redswoop/gi-joe-killer-whale/hatch/ref/ebay_hinge_closeup.jpeg

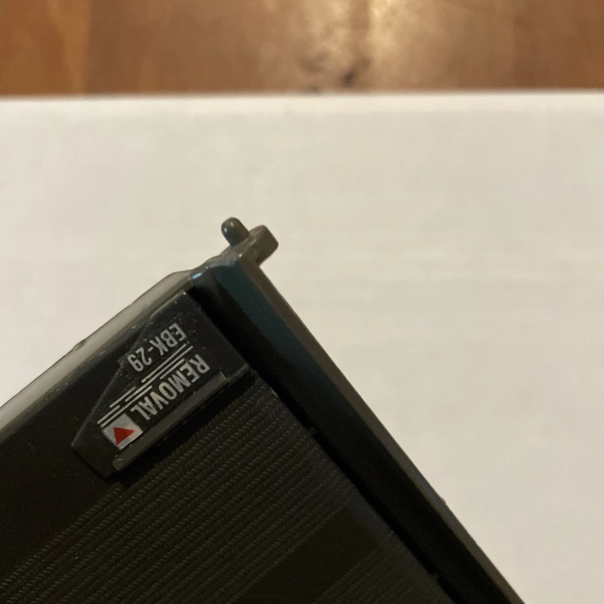
hatch/ref/ebay_hinge_closeup.jpeg
