redswoop/gi-joe-killer-whale/hatch/ref/ebay_outer_face.jpeg

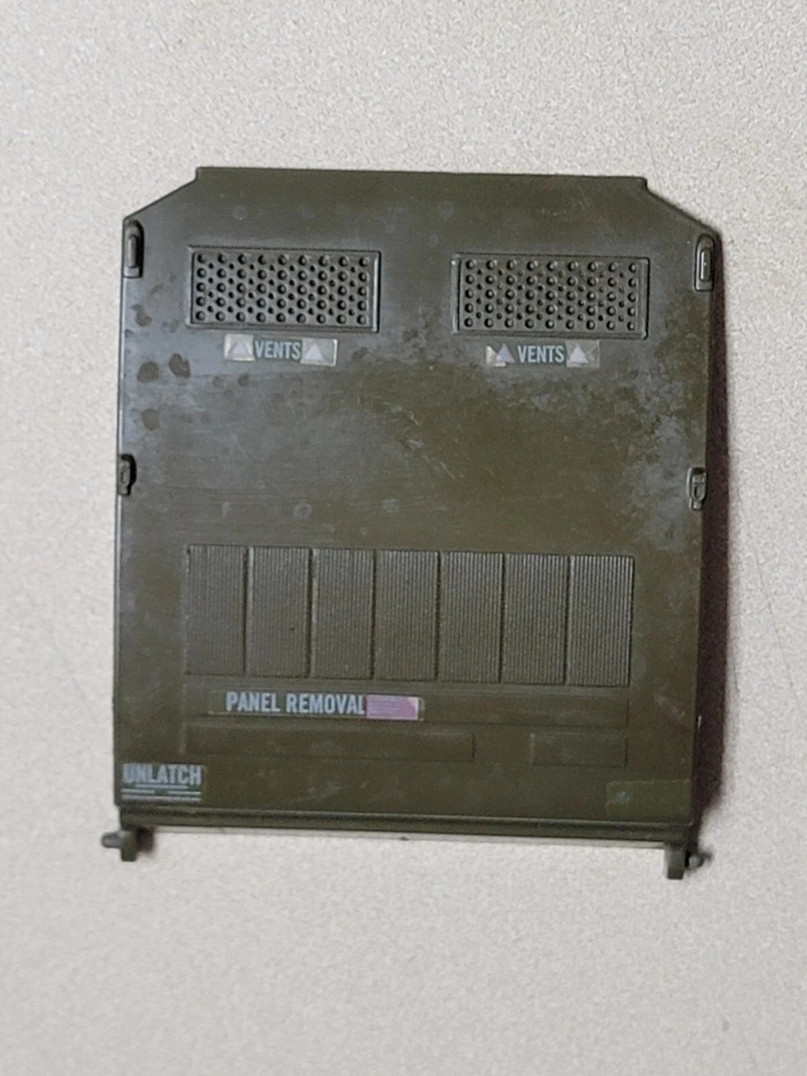
hatch/ref/ebay_outer_face.jpeg
