redswoop/gi-joe-killer-whale/hatch/ref/hull_photo_4.jpeg

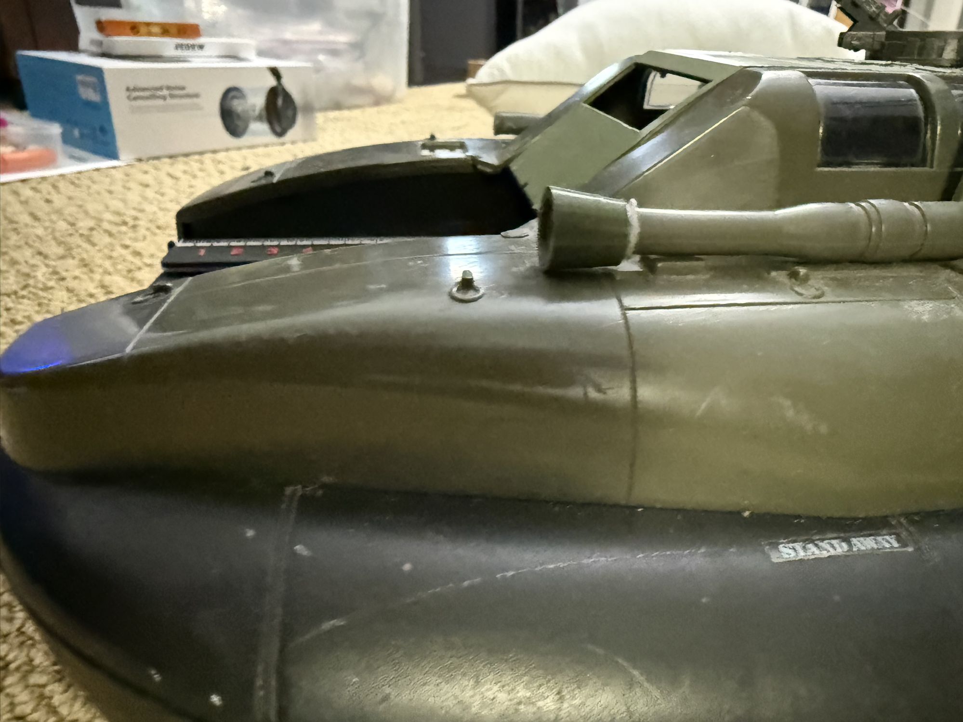
hatch/ref/hull_photo_4.jpeg
