redswoop/gi-joe-killer-whale/hatch/ref/profile_tracing.jpeg

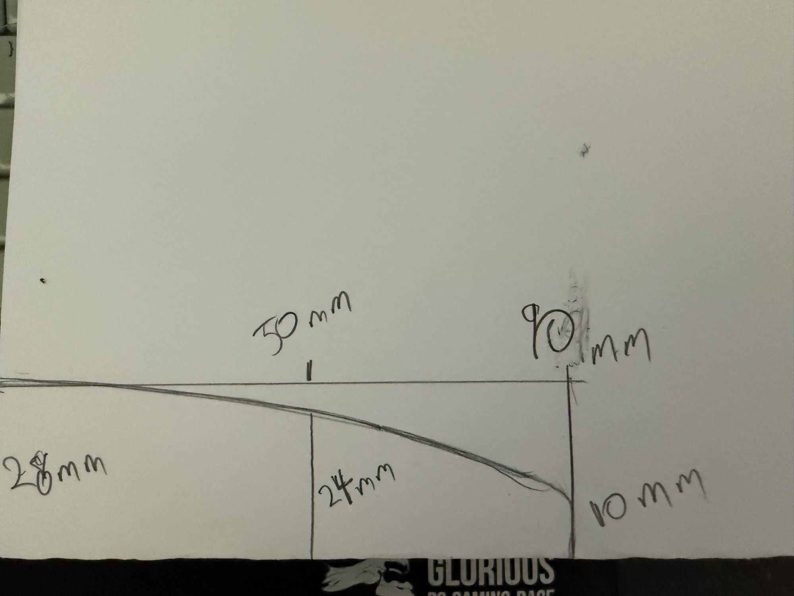
hatch/ref/profile_tracing.jpeg
