redswoop/gi-joe-killer-whale/shroud/stl/vane_right_filpin.stl

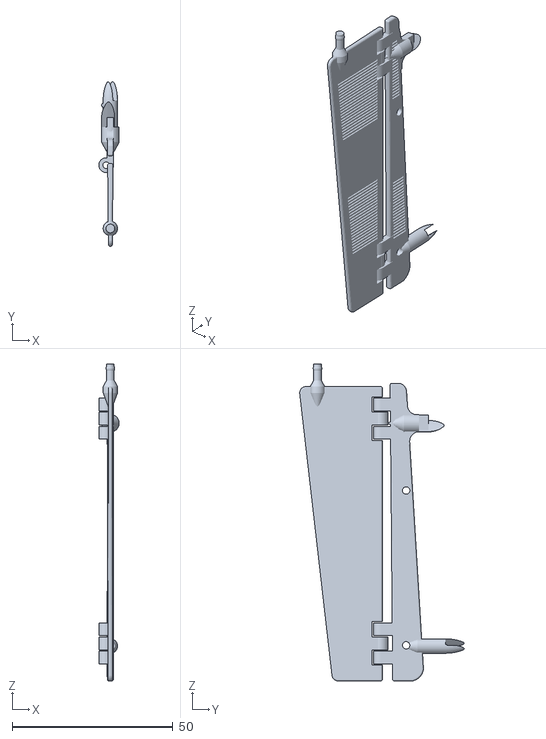
[picture p25: CAD file, 2026-09-13]
shroud/stl/vane_right_filpin.stl
6.35 x 51.3 x 98.7
