redswoop/gi-joe-killer-whale/shroud/stl/hinge_coupon.stl

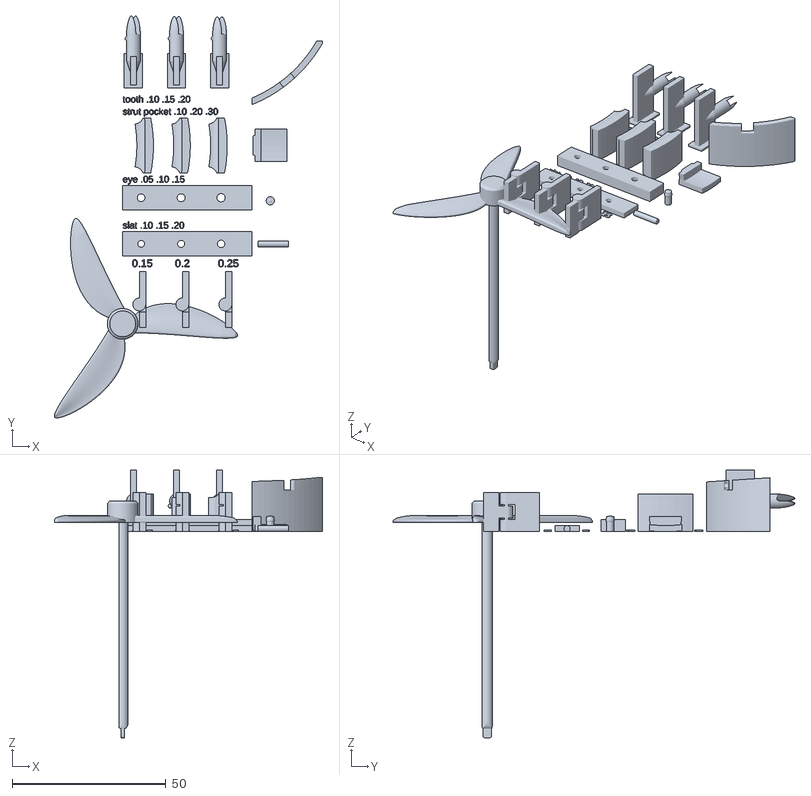
[picture p26: CAD file, 2026-09-12]
shroud/stl/hinge_coupon.stl
87.2 x 130.7 x 87.0
