redswoop/gi-joe-killer-whale/shroud/stl/hinge_coupon_filpin.stl

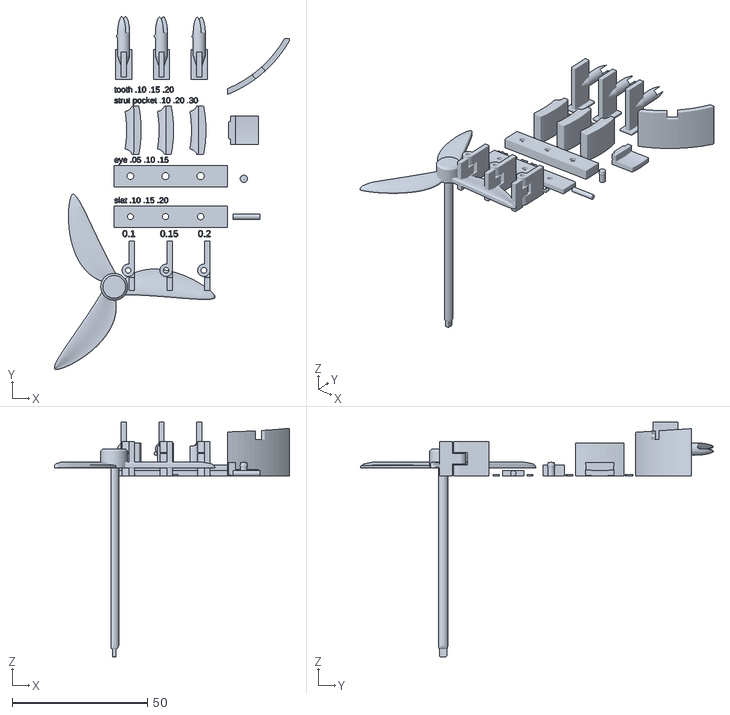
[picture p27: CAD file, 2026-09-12]
shroud/stl/hinge_coupon_filpin.stl
87.2 x 130.7 x 87.0
