redswoop/gi-joe-killer-whale/shroud/stl/tab_coupon.stl

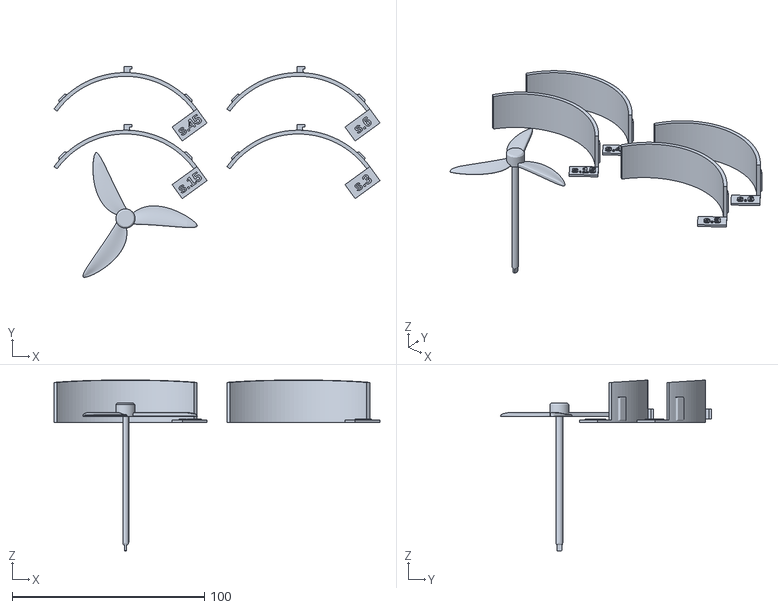
[picture p28: CAD file, 2026-09-12]
shroud/stl/tab_coupon.stl
169.7 x 109.7 x 89.0
