redswoop/gi-joe-killer-whale/shroud/stl/shaft.stl

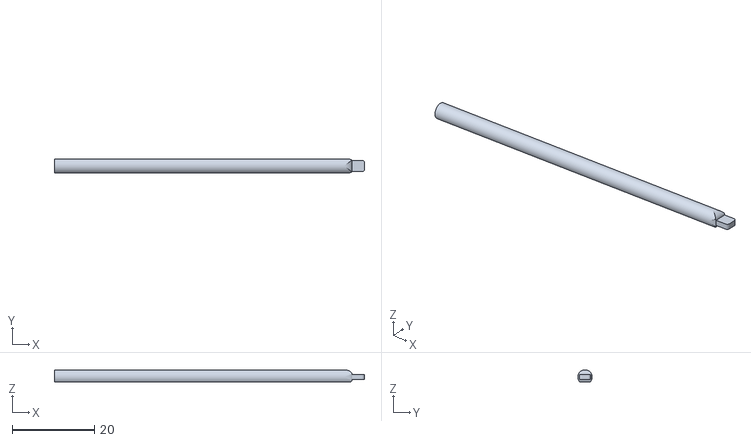
[picture p29: CAD file, 2026-09-12]
shroud/stl/shaft.stl
75.5 x 3.50 x 3.00
