redswoop/gi-joe-killer-whale/shroud/stl/fan.stl

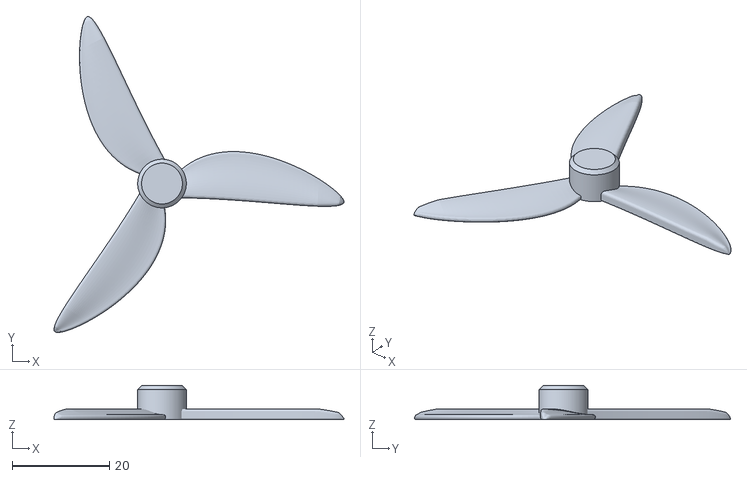
[picture p30: CAD file, 2026-09-12]
shroud/stl/fan.stl
59.6 x 65.0 x 7.00
