redswoop/gi-joe-killer-whale/shroud/stl/slat_fused.stl

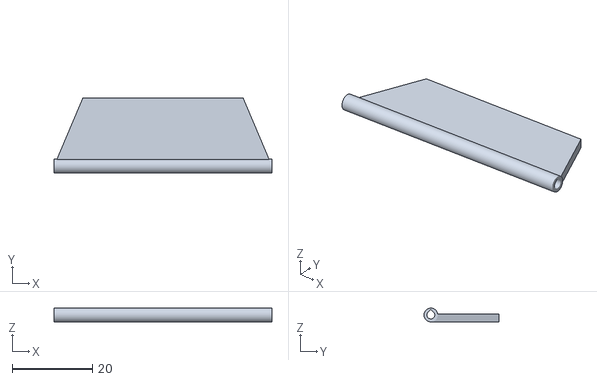
[picture p31: CAD file, 2026-09-12]
shroud/stl/slat_fused.stl
54.4 x 18.7 x 3.45
