redswoop/gi-joe-killer-whale/shroud/stl/shroud_saddle.stl

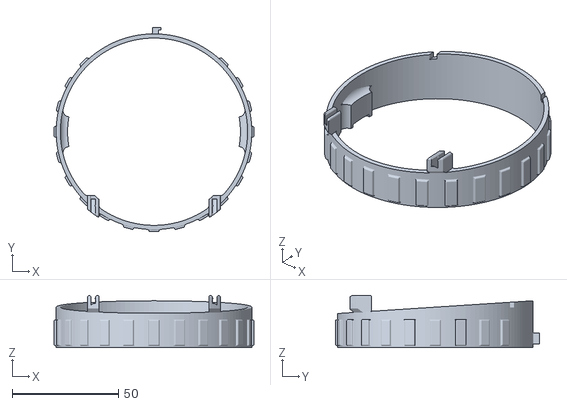
[picture p32: CAD file, 2026-09-11]
shroud/stl/shroud_saddle.stl
94.0 x 96.1 x 24.5
