redswoop/gi-joe-killer-whale/shroud/stl/tie_bar.stl

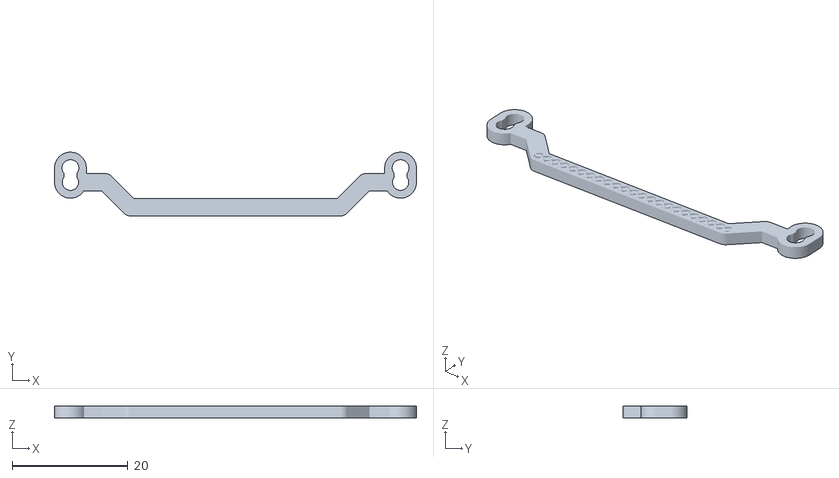
[picture p33: CAD file, 2026-09-11]
shroud/stl/tie_bar.stl
62.5 x 11.0 x 2.00
