redswoop/gi-joe-killer-whale/shroud/stl/slat.stl

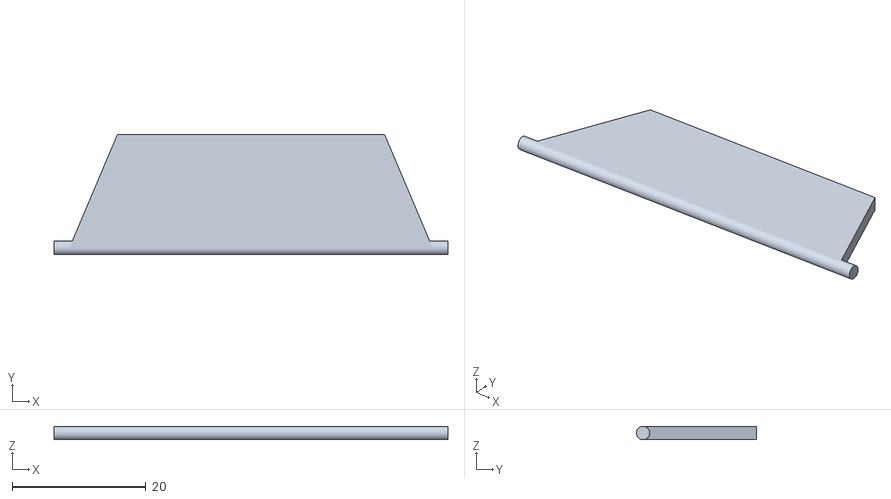
[picture p34: CAD file, 2026-09-11]
shroud/stl/slat.stl
59.0 x 18.0 x 2.00
