redswoop/gi-joe-killer-whale/shroud/stl/strut.3mf

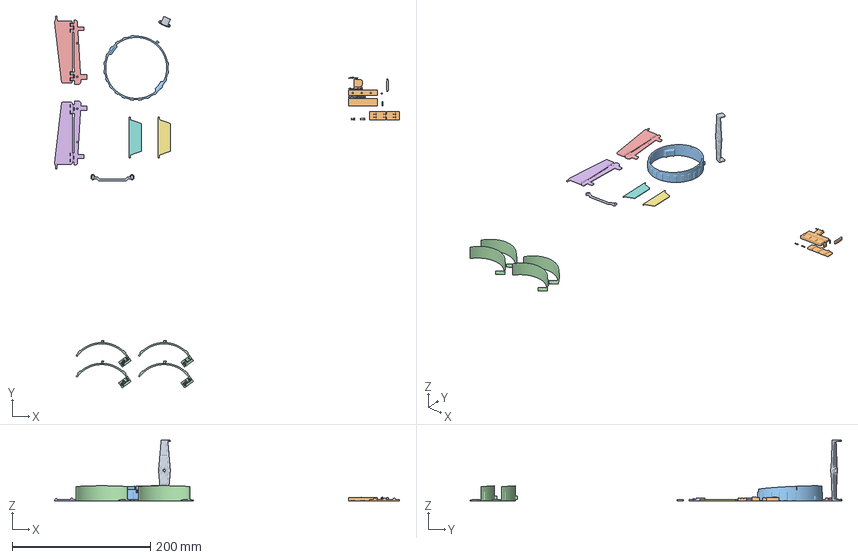
[picture p35: CAD file, 2026-09-11]
shroud/stl/strut.3mf
498.8 x 537.6 x 88.0 mm
strut.stl
hinge_coupon.stl
shroud.stl
tab_coupon.stl
vane_left.stl
vane_right.stl
slat.stl x 2
tie_bar.stl
