redswoop/gi-joe-killer-whale/shroud/check.scad

// Collision checks for the steering mechanism. Each `pair` should be EMPTY.
//   pair: "fins-roots" | "fins-duct" | "roots-duct" | "tie-fins" | "fins-fins" | "tie-duct" | "slats-fins" | "slats-roots" | "slats-duct" | "strut-duct" | "fan-duct" | "fan-strut" | "fan-roots" | "shaft-strut"
// Run with -D steer=<deg>. An empty export (84-byte STL) means no collision.
// vane_mount = "fused": "roots-duct" is skipped (they are one body by design); "slats-roots" then includes the filament axles.
include <shroud.scad>
show_ghost = false; show_shroud = false; show_strut = false; show_vanes = false; show_fan = false;
pair = "fins-roots";
strut_dz = 0;       // strut pose: 0 = seated against the pocket ceilings, >0 = pulled down that far while sliding in
module A() {
    if (pair == "fan-duct" || pair == "fan-strut" || pair == "fan-roots") fan_placed();
    if (pair == "shaft-strut") shaft_placed();
    if (pair == "strut-duct") translate([0, 0, -strut_dz]) strut();
    if (pair == "slats-fins" || pair == "slats-roots" || pair == "slats-duct") slats();
    if (pair == "fins-roots" || pair == "fins-duct" || pair == "fins-fins") vane_fins();
    if (pair == "roots-duct" && !fused) vane_roots();
    if (pair == "tie-fins" || pair == "tie-duct") tie_bar_placed();
}
module B() {
    if (pair == "fan-duct") { duct(); deco_boxes(); tab(); }
    if (pair == "fan-strut" || pair == "shaft-strut") translate([0, 0, -strut_dz]) strut();
    if (pair == "fan-roots") vane_roots();
    if (pair == "strut-duct") { duct(); deco_boxes(); tab(); }
    if (pair == "slats-fins") vane_fins();
    if (pair == "slats-roots") vane_roots();
    if (pair == "slats-duct") { duct(); deco_boxes(); tab(); }
    if (pair == "fins-roots") vane_roots();
    if (pair == "fins-duct" || pair == "roots-duct" || pair == "tie-duct") { duct(); deco_boxes(); tab(); }
    if (pair == "tie-fins") vane_fins();
    if (pair == "fins-fins") place_fin(-1);      // vs place_fin(1) inside A: they only collide if they cross the centreline
}
if (pair == "fins-fins") intersection() { place_fin(1); place_fin(-1); }
else intersection() { A(); B(); }
